hexwell/power-meter/pcb/power_meter.sch

## KiCad design pcb/power_meter.sch (2021-12-27, an earlier design)

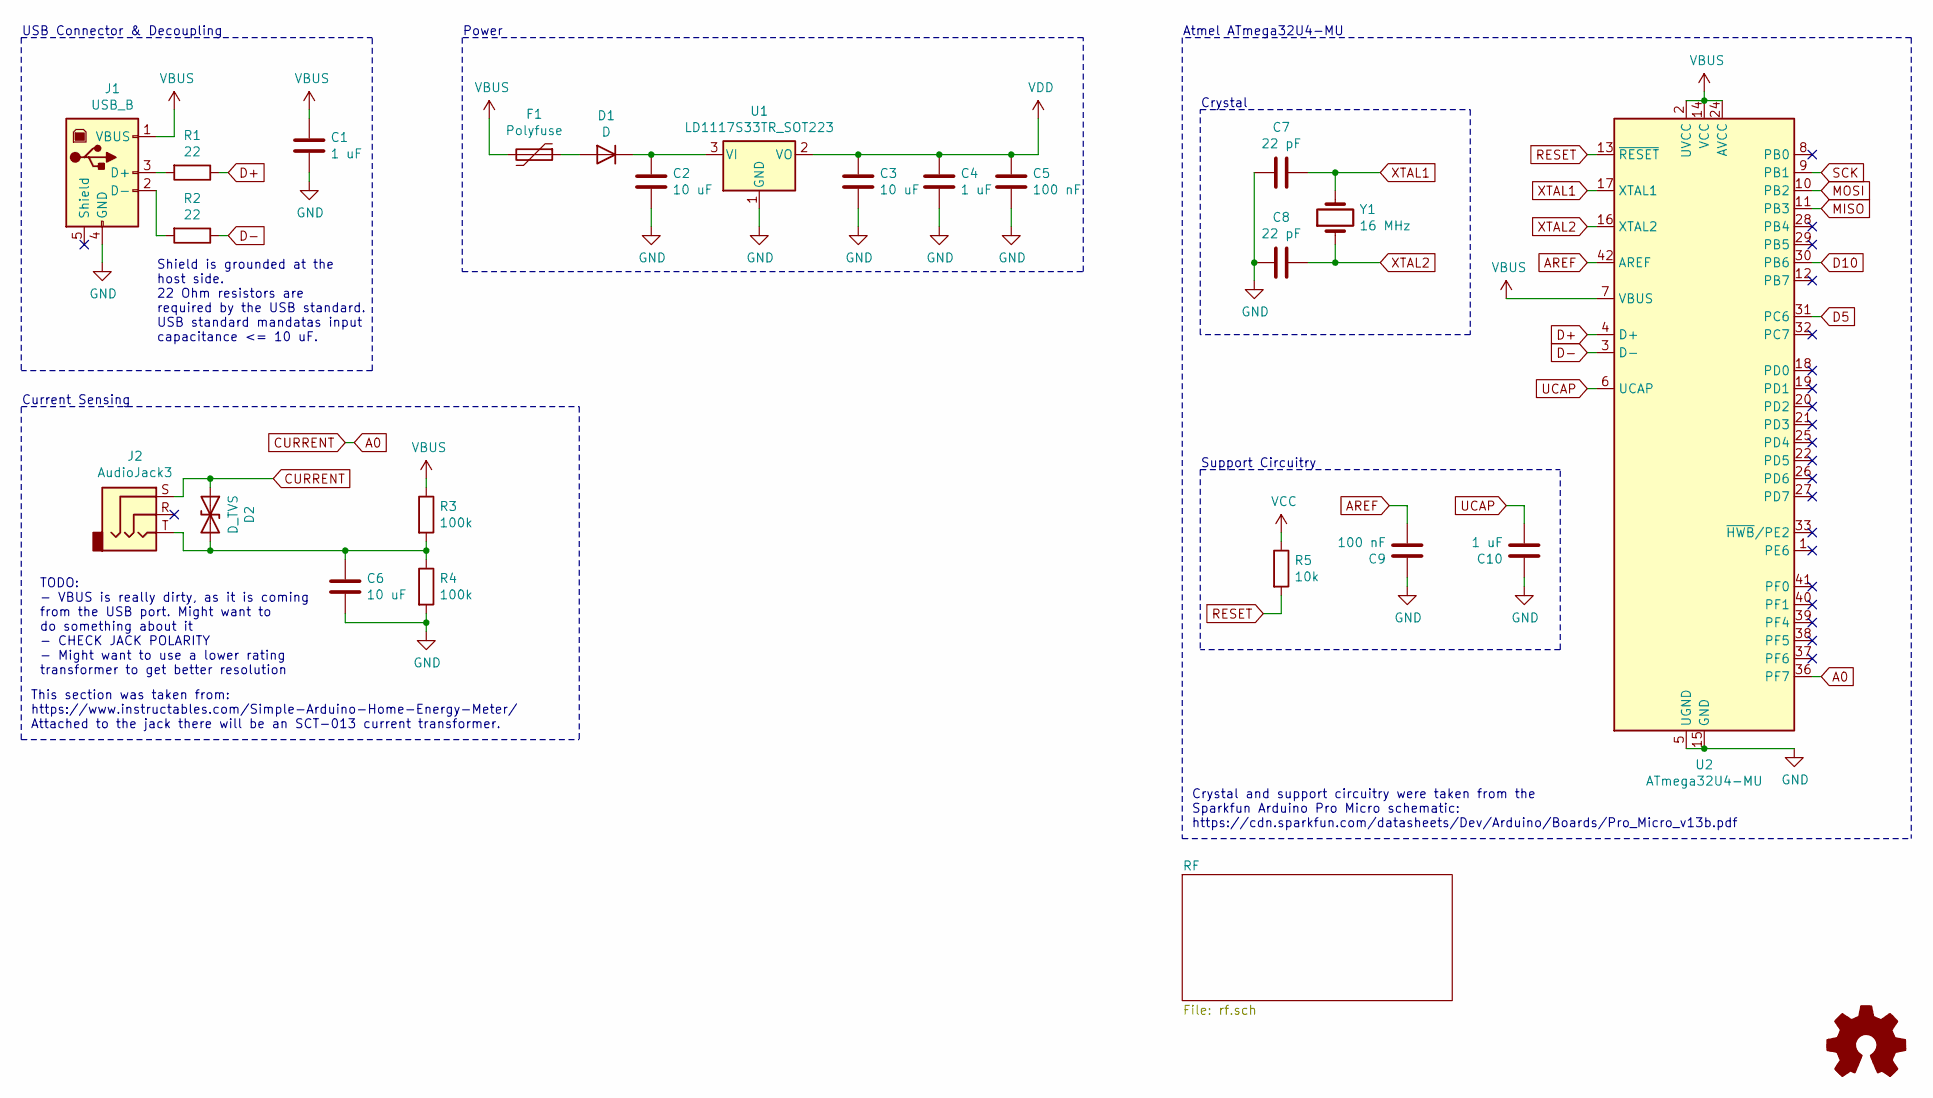
[picture p3: schematic power_meter.sch]

Parts:
C1, C4: 1 uF
C2, C3, C6: 10 uF
C5: 100 nF
C7, C8: 22 pF; C_0402_1005Metric
C9: 100 nF; C_0402_1005Metric
C10: 1 uF; C_0402_1005Metric
D1: D
D2: D_TVS
F1: Polyfuse
J1: USB_B; USB_B_Lumberg_2411_02_Horizontal
J2: AudioJack3; Jack_3.5mm_CUI_SJ-3523-SMT_Horizontal
LOGO1: Logo_Open_Hardware_Small; OSHW-Logo2_9.8x8mm_SilkScreen
R1, R2: 22
R3, R4: 100k
R5: 10k; R_0402_1005Metric
U1: LD1117S33TR_SOT223; SOT-223-3_TabPin2
U2: ATmega32U4-MU; QFN-44-1EP_7x7mm_P0.5mm_EP5.2x5.2mm
Y1: 16 MHz

Connections:
A0: D2.1 (A1), J2.S, U2.36 (PF7)
AREF: C9.2, U2.42 (AREF)
D5: U2.31 (PC6)
D10: U2.30 (PB6)
D+: R1.1, U2.4 (D+)
D-: R2.1, U2.3 (D-)
GND: C1.2, C2.2, C3.2, C4.2, C5.2, C6.2, C7.2, C8.2, C9.1, C10.1, J1.4 (GND), R4.2, U1.1 (GND), U2.5 (UGND), U2.15 (GND), U2.23 (GND), U2.35 (GND), U2.43 (GND), U2.45 (GND)
MISO: U2.11 (PB3)
MOSI: U2.10 (PB2)
unnamed: C2.1, D1.1 (K), U1.3 (VI)
unnamed: C6.1, D2.2 (A2), J2.T, R3.2, R4.1
unnamed: D1.2 (A), F1.1
unnamed: J1.2 (D-), R2.2
unnamed: J1.3 (D+), R1.2
RESET: R5.2, U2.13 (~RESET)
SCK: U2.9 (PB1)
UCAP: C10.2, U2.6 (UCAP)
VBUS: C1.1, F1.2, J1.1 (VBUS), R3.1, U2.2 (UVCC), U2.7 (VBUS), U2.14 (VCC), U2.24 (AVCC), U2.34 (VCC), U2.44 (AVCC)
VCC: R5.1
VDD: C3.1, C4.1, C5.1, U1.2 (VO)
XTAL1: C7.1, U2.17 (XTAL1), Y1.2
XTAL2: C8.1, U2.16 (XTAL2), Y1.1

Notes on the sheet:
USB Connector & Decoupling
Shield is grounded at the host side. 22 Ohm resistors are required by the USB standard. USB standard mandatas input capacitance <= 10 uF.
Atmel ATmega32U4-MU
Crystal
Support Circuitry
Crystal and support circuitry were taken from the Sparkfun Arduino Pro Micro schematic: https://cdn.sparkfun.com/datasheets/Dev/Arduino/Boards/Pro_Micro_v13b.pdf
TODO: - VBUS is really dirty, as it is coming from the USB port. Might want to do something about it - CHECK JACK POLARITY - Might want to use a lower rating transformer to get better resolution
This section was taken from: https://www.instructables.com/Simple-Arduino-Home-Energy-Meter/ Attached to the jack there will be an SCT-013 current transformer.
Current Sensing
Power
