hexwell/power-meter/pcb/rf.sch

## KiCad design pcb/rf.sch (2021-12-27, an earlier design)

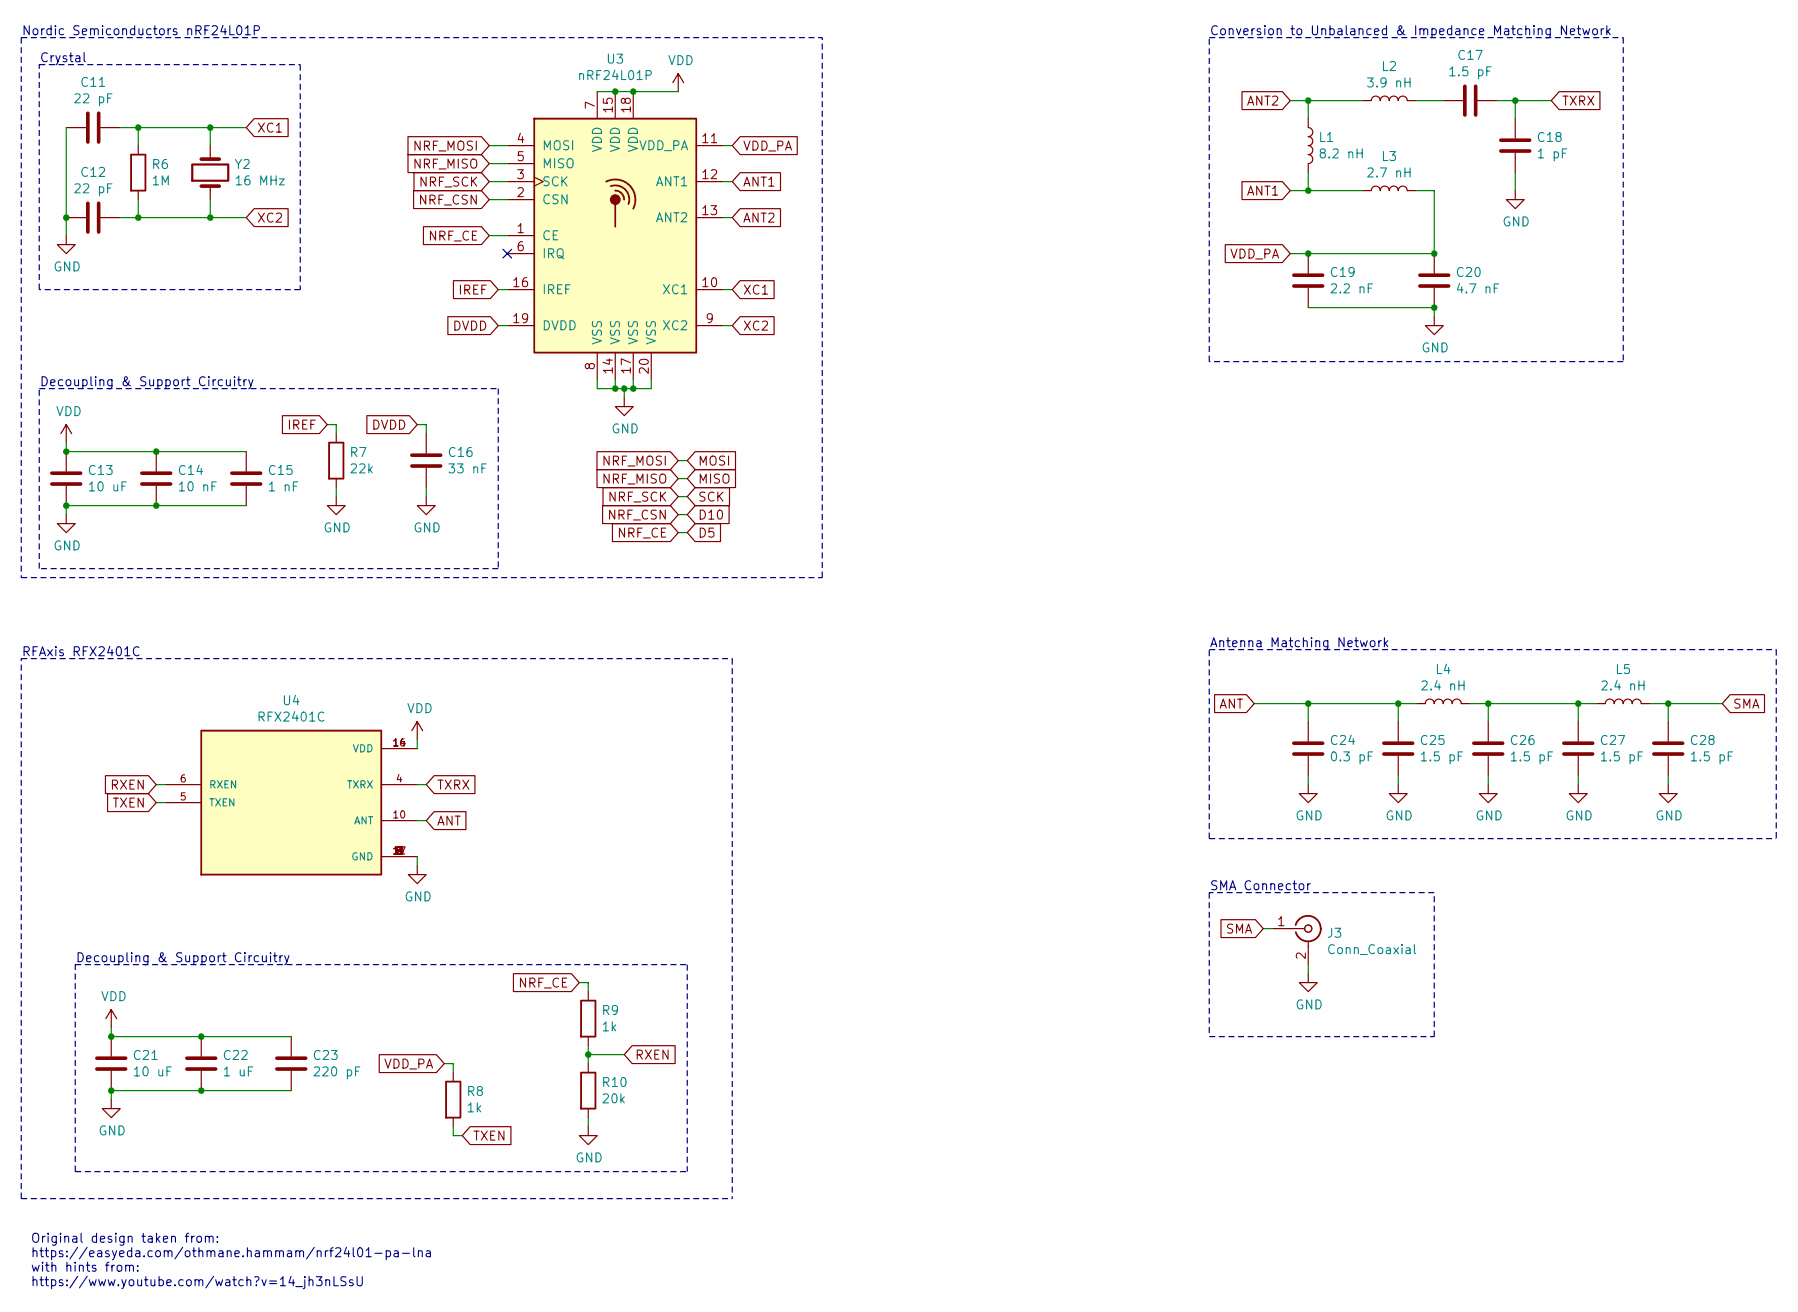
[picture p4: schematic rf.sch]

Parts:
C11, C12: 22 pF; C_0402_1005Metric
C13, C21: 10 uF; C_0402_1005Metric
C14: 10 nF; C_0402_1005Metric
C15: 1 nF; C_0402_1005Metric
C16: 33 nF; C_0402_1005Metric
C17, C25, C26, C27, C28: 1.5 pF; C_0402_1005Metric
C18: 1 pF; C_0402_1005Metric
C19: 2.2 nF; C_0402_1005Metric
C20: 4.7 nF; C_0402_1005Metric
C22: 1 uF; C_0402_1005Metric
C23: 220 pF; C_0402_1005Metric
C24: 0.3 pF; C_0402_1005Metric
J3: Conn_Coaxial; SMA_Amphenol_132203-12_Horizontal
L1: 8.2 nH; L_0402_1005Metric
L2: 3.9 nH; L_0402_1005Metric
L3: 2.7 nH; L_0402_1005Metric
L4, L5: 2.4 nH; L_0402_1005Metric
R6: 1M; R_0402_1005Metric
R7: 22k; R_0402_1005Metric
R8, R9: 1k; R_0402_1005Metric
R10: 20k; R_0402_1005Metric
U3: nRF24L01P; QFN-20-1EP_4x4mm_P0.5mm_EP2.5x2.5mm
U4: RFX2401C; QFN50P300X300X60-17N
Y2: 16 MHz

Connections:
ANT: C24.1, C25.1, L4.1, U4.10 (ANT)
ANT1: L1.2, L3.1, U3.12 (ANT1)
ANT2: L1.1, L2.1, U3.13 (ANT2)
D5: R9.1, U3.1 (CE)
D10: U3.2 (CSN)
DVDD: C16.1, U3.19 (DVDD)
GND: C11.2, C12.2, C13.2, C14.2, C15.2, C16.2, C18.2, C19.2, C20.2, C21.2, C22.2, C23.2, C24.2, C25.2, C26.2, C27.2, C28.2, J3.2 (Ext), R7.2, R10.2, U3.8 (VSS), U3.14 (VSS), U3.17 (VSS), U3.20 (VSS), U4.2 (GND), U4.3 (GND), U4.8 (GND), U4.9 (GND), U4.11 (GND), U4.17 (GND)
IREF: R7.1, U3.16 (IREF)
MISO: U3.5 (MISO)
MOSI: U3.4 (MOSI)
NRF_SCK: U3.3 (SCK)
unnamed: C17.2, L2.2
unnamed: C26.1, C27.1, L4.2, L5.1
RXEN: R9.2, R10.1, U4.6 (RXEN)
SMA: C28.1, J3.1 (In), L5.2
TXEN: R8.2, U4.5 (TXEN)
TXRX: C17.1, C18.1, U4.4 (TXRX)
VDD: C13.1, C14.1, C15.1, C21.1, C22.1, C23.1, U3.7 (VDD), U3.15 (VDD), U3.18 (VDD), U4.14 (VDD), U4.16 (VDD)
VDD_PA: C19.1, C20.1, L3.2, R8.1, U3.11 (VDD_PA)
XC1: C11.1, R6.1, U3.10 (XC1), Y2.2
XC2: C12.1, R6.2, U3.9 (XC2), Y2.1

Notes on the sheet:
Conversion to Unbalanced & Impedance Matching Network
Decoupling & Support Circuitry
RFAxis RFX2401C
Crystal
Nordic Semiconductors nRF24L01P
Original design taken from: https://easyeda.com/othmane.hammam/nrf24l01-pa-lna with hints from: https://www.youtube.com/watch?v=14_jh3nLSsU
Antenna Matching Network
SMA Connector
